Befaco/midithing/firmware/MIDIClass.h

// Copyright 2014 Sergio Retamero.
//
// Author: Sergio Retamero (sergio.retamero@gmail.com)
//
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
// See http://creativecommons.org/licenses/MIT/ for more information.
//
// -----------------------------------------------------------------------------
//
// bitfield implementation adapted from
// http://stackoverflow.com/questions/1590893/error-trying-to-define-a-1-024-bit-128-byte-bit-field

#include "firmware.h"
#include "MultiPointConv.h"
#include "BitField128.h"

void AllNotesOff(void);
int ReadMIDIeeprom(void);
void WriteMIDIeeprom(void);
void SetVoiceMode(int mode);
// Learn mode
void DoLearnCycle(void);
void EnterLearnMode(void);
// Calibration mode
void DoCalCycle(void);
void EnterCalMode(void);
void EndCalMode(void);
byte CalProcessNote(byte channel, byte pitch, byte velocity);
int PercussionNoteGate(byte pitch);

//MIDI
class MIDICV;
extern MIDICV Voice[4]; // Define up to four MIDI channels
extern int NumVoices; // Number of MIDI channels in use
extern int VoiceMode; // MIDI mode Set to quad mode by default

#define MAXNOTES 8

static bool IsPolyMode() {
  return (VoiceMode == POLYFIRST
          || VoiceMode == POLYLAST
          || VoiceMode == POLYHIGH
          || VoiceMode == POLYLOW);
}

static bool IsPercMode() {
  return (VoiceMode == PERCTRIG || VoiceMode == PERCGATE);
}

struct NoteEvent {
public:
  byte pitch;
  byte velocity;
};

class NoteEventInfo {
public:
  bool isPlaying(byte pitch) {
    return isbitset128(noteField_, (size_t)pitch);
  }

  byte setPlaying(byte pitch, byte velocity) {
    if (velocity) {
      if (!isbitset128(noteField_, (size_t)pitch) && count_ < MAXNOTES) {
        setbit128(noteField_, (size_t)pitch);
        events_[count_++] = { pitch, velocity };
      }
    }
    else {
      if (isbitset128(noteField_, (size_t)pitch)) {
        unsetbit128(noteField_, (size_t)pitch);
        // Remove note from the list
        for (int i = 0; i < count_; i++) {
          if (events_[i].pitch == pitch) {
            while (i < count_) {
              events_[i] = events_[i + 1];
              i++;
            }
            break;
          }
        }
        count_--;
      }
    }
    return count_;
  }

  byte setPlayingFront(byte pitch, byte velocity) {
    if (velocity) {
      if (!isbitset128(noteField_, (size_t)pitch) && count_ < MAXNOTES) {
        setbit128(noteField_, (size_t)pitch);
        for (int i = count_ - 1; i >= 0; i--) {
          events_[i + 1] = events_[i];
        }
        events_[0] = { pitch, velocity };
        count_++;
      }
      return count_;
    }
    else return setPlaying(pitch, velocity);
  }

  byte getCount() { return count_; }

  bool getEvent(byte idx, byte* pitch, byte* velocity = nullptr) {
    if (!count_ || idx >= count_) {
      *pitch = 0;
      if (velocity) *velocity = 0;
      return false;
    }
    *pitch = events_[idx].pitch;
    if (velocity) *velocity = events_[idx].velocity;
    return true;
  }

  bool getLastEvent(byte* pitch, byte* velocity = nullptr) {
    return getEvent(count_ - 1, pitch, velocity);
  }

  void clear() {
    count_ = 0;
    clearbitset128(noteField_);
  }

private:
  byte count_ = 0;
  BitField128 noteField_ = {0}; // more efficient than iterating list
  NoteEvent events_[MAXNOTES] = {};
};

class MIDICV {

//////////////////////////////////////////////
//Variables
public:
  // Var MIDI
  byte midiChannel = 1; // Initial channel
  byte gatePin = PINGATE;
  NoteEventInfo notes;
  // Var MIDI-DAC
  class MultiPointConv *pitchDAC, *velDAC, *bendDAC, *modDAC;

//////////////////////////////////////////////
// Function declaration
  MIDICV() {}

  void processNoteOn(byte pitch, byte velocity);
  void processNoteOff(byte pitch);
  void processBend(int bend);
  void processMod(byte value);
#ifdef PRINTDEBUG
  void printNotes(void);
#endif
  byte checkRepeat(byte pitch);
  void playNote(byte note, byte plvelocity);
  void playNoteOff(void);
  void LearnThis(byte channel, byte pitch, byte velocity);
  bool isPlayingNote(byte pitch) { return notes.isPlaying(pitch); }
};

class VoiceSelector {
public:

  void clear()
  {
    playing_.clear();
    pool_.clear();
  }

  void noteOn(int channel, byte pitch, byte velocity)
  {
    Voice[channel].processNoteOn(pitch, velocity);
    addToPlaying(pitch);
  }

  void noteOff(int channel, byte pitch)
  {
    Voice[channel].processNoteOff(pitch);
    removeFromPlaying(pitch);
    if (IsPolyMode() && popNextNoteFromPool(&pitch)) {
      Voice[channel].processNoteOn(pitch, 64);
      if (VoiceMode == POLYLAST) {
        // the note being pulled from the pool will be older than anything playing
        addToPlayingFront(pitch);
      }
      else {
        addToPlaying(pitch);
      }
    }
  }

  // Check if received channel is any active MIDI
  int getTargetChannel(byte channel, byte pitch = 0, byte velocity = 0)
  {
    // If in percussion mode, check the note and return the associated gate
    if (IsPercMode() && channel == 10) {
      return (PercussionNoteGate(pitch));
    }

    if (IsPolyMode()) {
      return getPolyTargetChannel(channel, pitch, velocity);
    }

    // In other modes, check if received one is an active channel
    for (int i = 0; i < NumVoices; i++) {
      if (Voice[i].midiChannel == channel && Voice[i].pitchDAC->minInput < pitch) {
        return (i);
      }
    }
    return (-1);
  }

private:

  bool popNextNoteFromPool(byte* pitch, byte* velocity = nullptr)
  {
    int poolCount = pool_.getCount();
    byte nextNote = 0;

    *pitch = 0;
    if (velocity) *velocity = 0;

    if (!poolCount) return false;
    switch (VoiceMode) {
      case POLYFIRST:
        pool_.getEvent(0, pitch);
        removeFromPool(*pitch);
        return true;
        break;
      case POLYLAST:
        pool_.getLastEvent(pitch);
        removeFromPool(*pitch);
        return true;
        break;
      case POLYHIGH:
        nextNote = 0;
        for (int i = 0; i < poolCount; i++) {
          byte testNote;
          pool_.getEvent(i, &testNote);
          if (testNote > nextNote) {
            nextNote = testNote;
          }
        }
        *pitch = nextNote;
        removeFromPool(*pitch);
        return true;
        break;
      case POLYLOW:
        nextNote = 127;
        for (int i = 0; i < poolCount; i++) {
          byte testNote;
          pool_.getEvent(i, &testNote);
          if (testNote < nextNote) {
            nextNote = testNote;
          }
        }
        *pitch = nextNote;
        removeFromPool(*pitch);
        return true;
        break;
      default:
        return false;
    }
    return false;
  }

  void addToPlaying(byte pitch, byte velocity = 64)
  {
    if (IsPolyMode()) {
      playing_.setPlaying(pitch, velocity);
    }
  }

  void addToPlayingFront(byte pitch, byte velocity = 64)
  {
    if (IsPolyMode()) {
      playing_.setPlayingFront(pitch, velocity);
    }
  }

  void removeFromPlaying(byte pitch)
  {
    if (IsPolyMode()) {
      playing_.setPlaying(pitch, 0);
    }
  }

  void addToPool(byte pitch, byte velocity = 64)
  {
    if (IsPolyMode()) {
      pool_.setPlaying(pitch, velocity);
    }
  }

  void addToPoolFront(byte pitch, byte velocity = 64)
  {
    if (IsPolyMode()) {
      pool_.setPlayingFront(pitch, velocity);
    }
  }

  void removeFromPool(byte pitch)
  {
    if (IsPolyMode()) {
      pool_.setPlaying(pitch, 0);
    }
  }

  int getPolyLowTarget(byte channel, byte pitch, byte velocity)
  {
    byte highestPitch = 0;
    byte highestChannel = 0;

    for (int i = 0; i < NumVoices; i++) {
      if (Voice[i].notes.getCount() && Voice[i].midiChannel == channel) {
        byte testPitch;
        Voice[i].notes.getLastEvent(&testPitch); // should only be one
        if (testPitch > highestPitch) {
          highestPitch = testPitch;
          highestChannel = i;
        }
      }
    }

    if (pitch > highestPitch) {
      addToPool(pitch);
      return -1;
    }

    if (pitch < highestPitch) {
      Voice[highestChannel].processNoteOff(highestPitch); // TODO: verify that there's only one note per channel in this mode
      addToPool(highestPitch);
      removeFromPlaying(highestPitch);
      return highestChannel;
    }

    addToPool(pitch);
    return -1; // something went wrong
  }

  int getPolyHighTarget(byte channel, byte pitch, byte velocity)
  {
    byte lowestPitch = 127;
    byte lowestChannel = 0;

    for (int i = 0; i < NumVoices; i++) {
      if (Voice[i].notes.getCount() && Voice[i].midiChannel == channel) {
        byte testPitch;
        Voice[i].notes.getLastEvent(&testPitch); // should only be one
        if (testPitch < lowestPitch) {
          lowestPitch = testPitch;
          lowestChannel = i;
        }
      }
    }

    if (pitch < lowestPitch) {
      addToPool(pitch);
      return -1;
    }

    if (pitch > lowestPitch) {
      Voice[lowestChannel].processNoteOff(lowestPitch); // TODO: verify that there's only one note per channel in this mode
      addToPool(lowestPitch);
      removeFromPlaying(lowestPitch);
      return lowestChannel;
    }

    addToPool(pitch);
    return -1; // something went wrong
  }

  int getPolyLastTarget(byte channel, byte pitch, byte velocity)
  {
    // get playing_[0]
    // find the channel playing that pitch
    // send a noteoff to that channel
    // move playing_[0] to pool_ (it will be the newest note in pool_)
    // shift playing_ down
    // return the channel
    byte oldestPitch;
    byte oldestChannel = -1;

    if (!playing_.getEvent(0, &oldestPitch)) {
      // something went wrong, but let's add it to the pool
      addToPool(pitch);
      return -1;
    }

    for (int i = 0; i < NumVoices; i++) {
      if (Voice[i].midiChannel == channel) {
        byte testPitch;
        Voice[i].notes.getLastEvent(&testPitch); // should only be one
        if (testPitch == oldestPitch) {
          oldestChannel = i;
          break;
        }
      }
    }

    if (oldestChannel >= 0) {
      Voice[oldestChannel].processNoteOff(oldestPitch); // TODO: verify that there's only one note per channel in this mode
      addToPoolFront(oldestPitch);
      removeFromPlaying(oldestPitch);
      return oldestChannel;
    }

    addToPool(pitch);
    return -1; // something went wrong
  }

  int getPolyTargetChannel(byte channel, byte pitch, byte velocity)
  {
    // first check all channels for the note
    for (int i = 0; i < NumVoices; i++) {
      if (Voice[i].midiChannel == channel && Voice[i].isPlayingNote(pitch)) {
        return i;
      }
    }

    // then look for an empty channel
    for (int i = 0; i < NumVoices; i++) {
      if (Voice[i].midiChannel == channel && !Voice[i].notes.getCount()) {
        return i;
      }
    }

    if (!velocity) {
      removeFromPool(pitch); //cleanup
      return -1;
    }

    switch (VoiceMode) {
      case POLYFIRST: // the last-played note is added to the pool, available only if a channel is freed
        addToPool(pitch);
        return -1;
        break;
      case POLYLAST: // the last-played note replaces the oldest playing note
        return getPolyLastTarget(channel, pitch, velocity);
        break;
      case POLYHIGH:
        return getPolyHighTarget(channel, pitch, velocity);
        break;
      case POLYLOW:
        return getPolyLowTarget(channel, pitch, velocity);
        break;
      default: return -1;
    }
    // something went wrong
    return -1;
  }

  NoteEventInfo playing_;
  NoteEventInfo pool_;
};

extern VoiceSelector Selector;
