Befaco/midithing/firmware/MIDIHandle.ino

// Copyright 2014 Sergio Retamero.
//
// Author: Sergio Retamero (sergio.retamero@gmail.com)
//
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
// See http://creativecommons.org/licenses/MIT/ for more information.
//
// -----------------------------------------------------------------------------
//

//////////////////////////////////////////////
// MIDI function definitions
// Play a NOTE to the MCU outputs/DAC
// Do whatever you want when you receive a Note On.

VoiceSelector Selector;
static int countCLOCK = 1;
static int ppqnCLOCK = 24;
static byte MIDIRun = 0; // Set to 0 to init in stop condition

void HandleNoteOn(byte channel, byte pitch, byte velocity)
{
  int MIDIactive = -1;

  // If in learn mode, catch info
  if (LearnMode == ENTERLEARN && velocity > 0) {
    Voice[LearnStep].LearnThis(channel, pitch, velocity);
    return;
  }
  // If in cal mode, adjust notes
  if (LearnMode == ENTERCAL && velocity > 0) {
    if (channel < 6) {
      if (CalProcessNote(channel, pitch, velocity)) {
        return;  // do not play note if calibration key pressed
      }
    }
  }

  // Check if received channel is any active MIDI
  MIDIactive = Selector.getTargetChannel(channel, pitch, velocity);
  if (MIDIactive == -1) { // no channels available
#ifdef PRINTDEBUG
    Serial.println("Not active MIDI");
#endif
    return; // received channel not any active MIDI
  }
  if (VoiceMode == PERCTRIG && channel == 10 && velocity > 0) {
    // Play percussion
    Gates[MIDIactive].setBlink(TRIGPERCUSSION, 1, 1); // Play trigger
    Blink.setBlink(100, 1, 1, PINLED);  // Blink once every Note ON (not in CAL/LEARN mode)
    return;
  }

  if (velocity == 0) {
    // This acts like a NoteOff.
    HandleNoteOff(channel, pitch, velocity);
    return;
  }

  if (LearnMode != ENTERCAL) {
    Blink.setBlink(100, 1, 1, PINLED);  // Blink once every Note ON (not in CAL/LEARN mode)
  }
  Selector.noteOn(MIDIactive, pitch, velocity);
}

// Do whatever you want when you receive a Note Off.
void HandleNoteOff(byte channel, byte pitch, byte velocity)
{
  int MIDIactive = -1;

  if (LearnMode == ENTERLEARN) {
    return;  // Do not process while in Learn Mode
  }

  // Check if received channel is any active MIDI
  MIDIactive = Selector.getTargetChannel(channel, pitch);
  if (MIDIactive == -1) {
#ifdef PRINTDEBUG
    Serial.println("Not active MIDI");
#endif
    return; // received channel not any active MIDI
  }
  // Do nothing in percussion mode
  if (VoiceMode == PERCTRIG && channel == 10) {
    return;
  }

  Selector.noteOff(MIDIactive, pitch);
}

// Do whatever you want when you receive a Note On.
void HandlePitchBend(byte channel, int bend)
{
  int MIDIactive = -1;

  if (LearnMode == ENTERLEARN) {
    return;  // Do not process while in Learn Mode
  }

  // Check if received channel is any active MIDI
  MIDIactive = Selector.getTargetChannel(channel);
  if (MIDIactive == -1) {
    return;  // received channel not any active MIDI
  }

  Voice[MIDIactive].processBend(bend);
}

// Do whatever you want when you receive a Control Change
void HandleControlChange(byte channel, byte number, byte value)
{
  int MIDIactive = -1;

  if (LearnMode == ENTERLEARN) {
    return;  // Do not process while in Learn Mode
  }
  // Check if received channel is any active MIDI
  MIDIactive = Selector.getTargetChannel(channel);
  if (MIDIactive == -1) {
    return;  // received channel not any active MIDI
  }

  switch (number) {
  case 1:
    Voice[MIDIactive].processMod(value);
    break; // Handle only CC #1 = Modulation
  case 123:
    for (int i = 0; i < NumVoices; i++) {
      Voice[i].playNoteOff(); // All notes off received
      Voice[i].notes.clear(); // 0 notes on
    }
#ifdef PRINTDEBUG
    Serial.println("All Notes Off");
#endif
  default:
    return;
  }
}

#ifdef STARTSTOPCONT
// Handle MIDI Start/Stop/Continue
void HandleStart(void)
{
  MIDIRun = 1;
  countCLOCK = 0;
  Gates[9].setBlink(TRIGSTART, 1, 1);
  //digitalWrite(PINSTARTSTOP, HIGH);
#ifdef PRINTDEBUG
  Serial.println("MIDI Start");
#endif
}

void HandleContinue(void)
{
  MIDIRun = 1;
  countCLOCK = 0;
  Gates[9].setBlink(TRIGSTART, 1, 1);
//  digitalWrite(PINSTARTSTOP, HIGH);
#ifdef PRINTDEBUG
  Serial.println("MIDI Continue");
#endif
}

void HandleStop(void)
{
  MIDIRun = 0;
  countCLOCK = 0;
  //digitalWrite(PINSTARTSTOP, LOW);
#ifdef PRINTDEBUG
  Serial.println("MIDI Stop");
#endif
}

void HandleClock(void)
{
  //( !MIDIRun) return; // Only when MIDI run command received

  if (countCLOCK < ppqnCLOCK) {
    countCLOCK++;
  } else {
    countCLOCK = 1;
    // Send trigger to CLOCK port
    Gates[4].setBlink(TRIGCLOCK, 1, 1);
  }
  /*
     digitalWrite( PINCLOCK, HIGH);
     //digitalWrite( PINLED, HIGH);
     delayMicroseconds(2000); // 2 milliseconds delay
     digitalWrite( PINCLOCK, LOW);
     //digitalWrite( PINLED, LOW);
   */
}

#endif  //STARTSTOPCONT
