Befaco/midithing/firmware/MIDILearn.ino

// Copyright 2014 Sergio Retamero.
//
// Author: Sergio Retamero (sergio.retamero@gmail.com)
//
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
// See http://creativecommons.org/licenses/MIT/ for more information.
//
// -----------------------------------------------------------------------------

//# define ERRORCYCLES 30

//////////////////////////////////////////////
// Learn mode
// Learn Mode selected

// Initialize Learn Mode
void EnterLearnMode(void)
{
  // Set Learn mode flag
  LearnMode = ENTERLEARN;
  LearnStep = 0;
  // Init blinker
  Blink.setBlink(900, 100, -1, PINLED);

  // All Notes off
  AllNotesOff();

  // Init timer
  LearnInitTime = millis();
#ifdef PRINTDEBUG
  Serial.println("Init Learn Mode");
#endif
}

// Learn Mode Cycle function
void DoLearnCycle(void)
{
  unsigned long current = millis();

// 10 seconds learn time
  if (current > LearnInitTime + 10000) {
    // Set normal mode
    LearnMode = NORMALMODE;
    // Turn off LED blink
    Blink.setBlink(0, 0, 0);
    // Store value in EEPROM
    WriteMIDIeeprom();

#ifdef PRINTDEBUG
    Serial.println("End Learn Mode");
#endif
  }
}

//////////////////////////////
// Initialize Cal Mode
void EnterCalMode(void)
{
  // Set Learn mode flag
  LearnMode = ENTERCAL;
  // Init blinker
  Blink.setBlink(500, 500, -1, PINLED2);

  // All Notes off
  AllNotesOff();

  // Set mode to 4 channels
  SetVoiceMode(QUADMIDI);

  // Init timer
  LearnInitTime = millis();
#ifdef PRINTDEBUG
  Serial.println("Init Cal Mode");
#endif
}

// Cal Mode Cycle function
void DoCalCycle(void)
{
  unsigned long current = millis();

  // After 55 seconds without receiving a note, exit calibration
  if (current > LearnInitTime + 55000) {
#ifdef PRINTDEBUG
    Serial.print(LearnInitTime);
    Serial.print(" msec ");
    Serial.println(current);
    Serial.println("Time expired for Calibration");
#endif
    EndCalMode();
  }
}

void EndCalMode(void)
{
  // Set normal mode
  LearnMode = NORMALMODE;
  // Store in EEPROM
  WriteMIDIeeprom();
  // Turn off LED blink
  Blink.setBlink(0, 0, 0);
#ifdef PRINTDEBUG
  Serial.println("End Cal Mode");
#endif
}

byte CalProcessNote(byte channel, byte pitch, byte velocity)
{
  if (channel < 5) { // Channels 1-4 for DAC calibration 0-3
    return (DACConv[channel - 1].Processnote(channel, pitch, velocity));
  } else if (channel == 5) {
    // Channel 5 for setting modes
    switch (pitch) {
    case 0: // C
      SetVoiceMode(MONOMIDI);
      return (1);
      break;
    case 2: // D
      SetVoiceMode(DUALMIDI);
      return (1);
      break;
    case 4: // E
      SetVoiceMode(QUADMIDI);
      return (1);
      break;
    case 5: // F
      SetVoiceMode(PERCTRIG);
      return (1);
      break;
  /*
    case 6:
      SetVoiceMode(PERCGATE);
      break;
  */
    case 7: // G
      SetVoiceMode(POLYFIRST);
      return (1);
      break;
    case 9: // A
      SetVoiceMode(POLYLAST);
      return (1);
      break;
    case 11: // B
      SetVoiceMode(POLYHIGH);
      return (1);
      break;
    case 12: // C'
      SetVoiceMode(POLYLOW);
      return (1);
      break;
    default:
      return (0);
    }
  }
  return (0);
}
